bsfconception/WT32-SC01/Cases/V1.0/holder/Readme.md

The SVG file is ready to be cut by a CO2 laser

The design is ready for 3mm Acrylic sheet
