bsfconception/WT32-SC01/Cases/V1.0/3DPrint/readme.md

There 3 files are clean and compatible with Cura or Repetier slicer.
It includes 
- the main enclure 
- the back cover
- the washer between the WT32 and expansion board


Note : the washers are designed to fit to the brass inserts as shown in the picture below
