bsfconception/WT32-SC01/Cases/V1.1/Image3.jpg

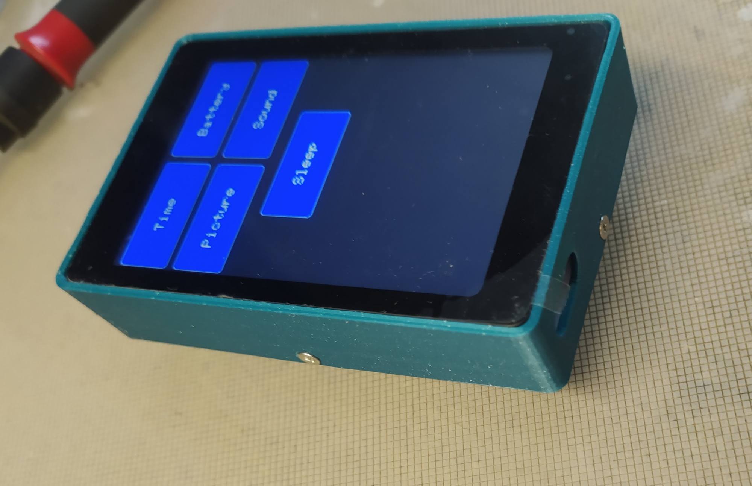
Cases/V1.1/Image3.jpg
