bsfconception/WT32-SC01/Versions/V1.0/PCB/Manufacturing/readme.md

These files have been used to manufacture the PCB usong JLCPCB services
