bsfconception/WT32-SC01/Versions/V1.2/Schematic/WT32-SC01.V1.2_Shematic.pdf

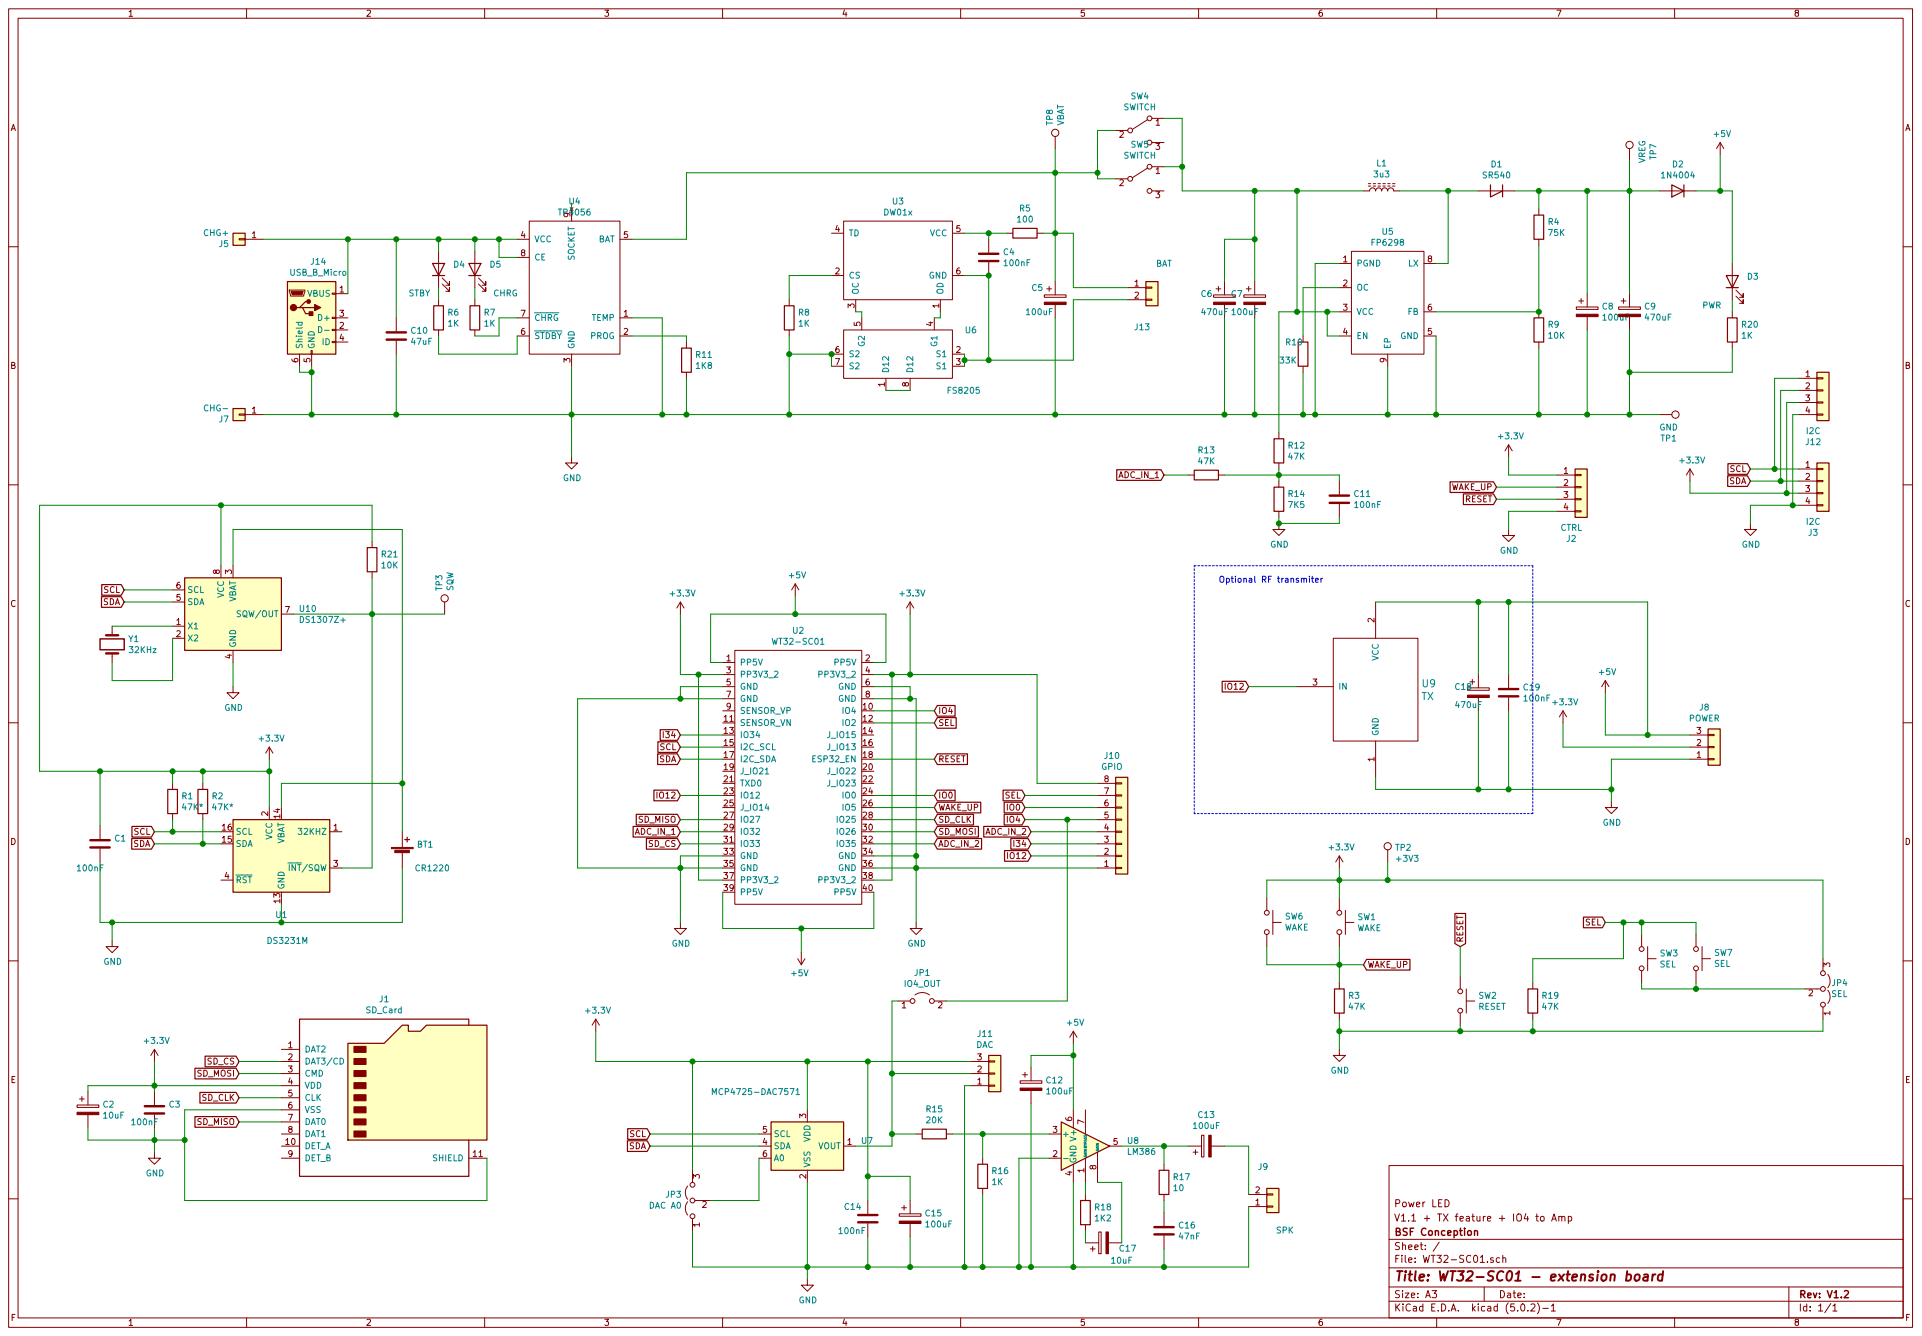
[picture p38: page 1]

3 VCC 4 BAT 5 STDBY 6 CHRG 7 CE 8 SOCKET

8 U6 FS8205 PGND 1 OC 2 VCC 3 EN 4 GND 5 FB 6

4 SDA 5 SCL 6 SQW/OUT 7 VCC

V1.1 + TX feature + IO4 to Amp Power LED

File: WT32-SC01.sch Sheet: / BSF Conception

Id: 1/1 Title: WT32-SC01 - extension board
