bsfconception/WT32-SC01/Versions/V1.0/Schematic/WT32-SC01.pdf

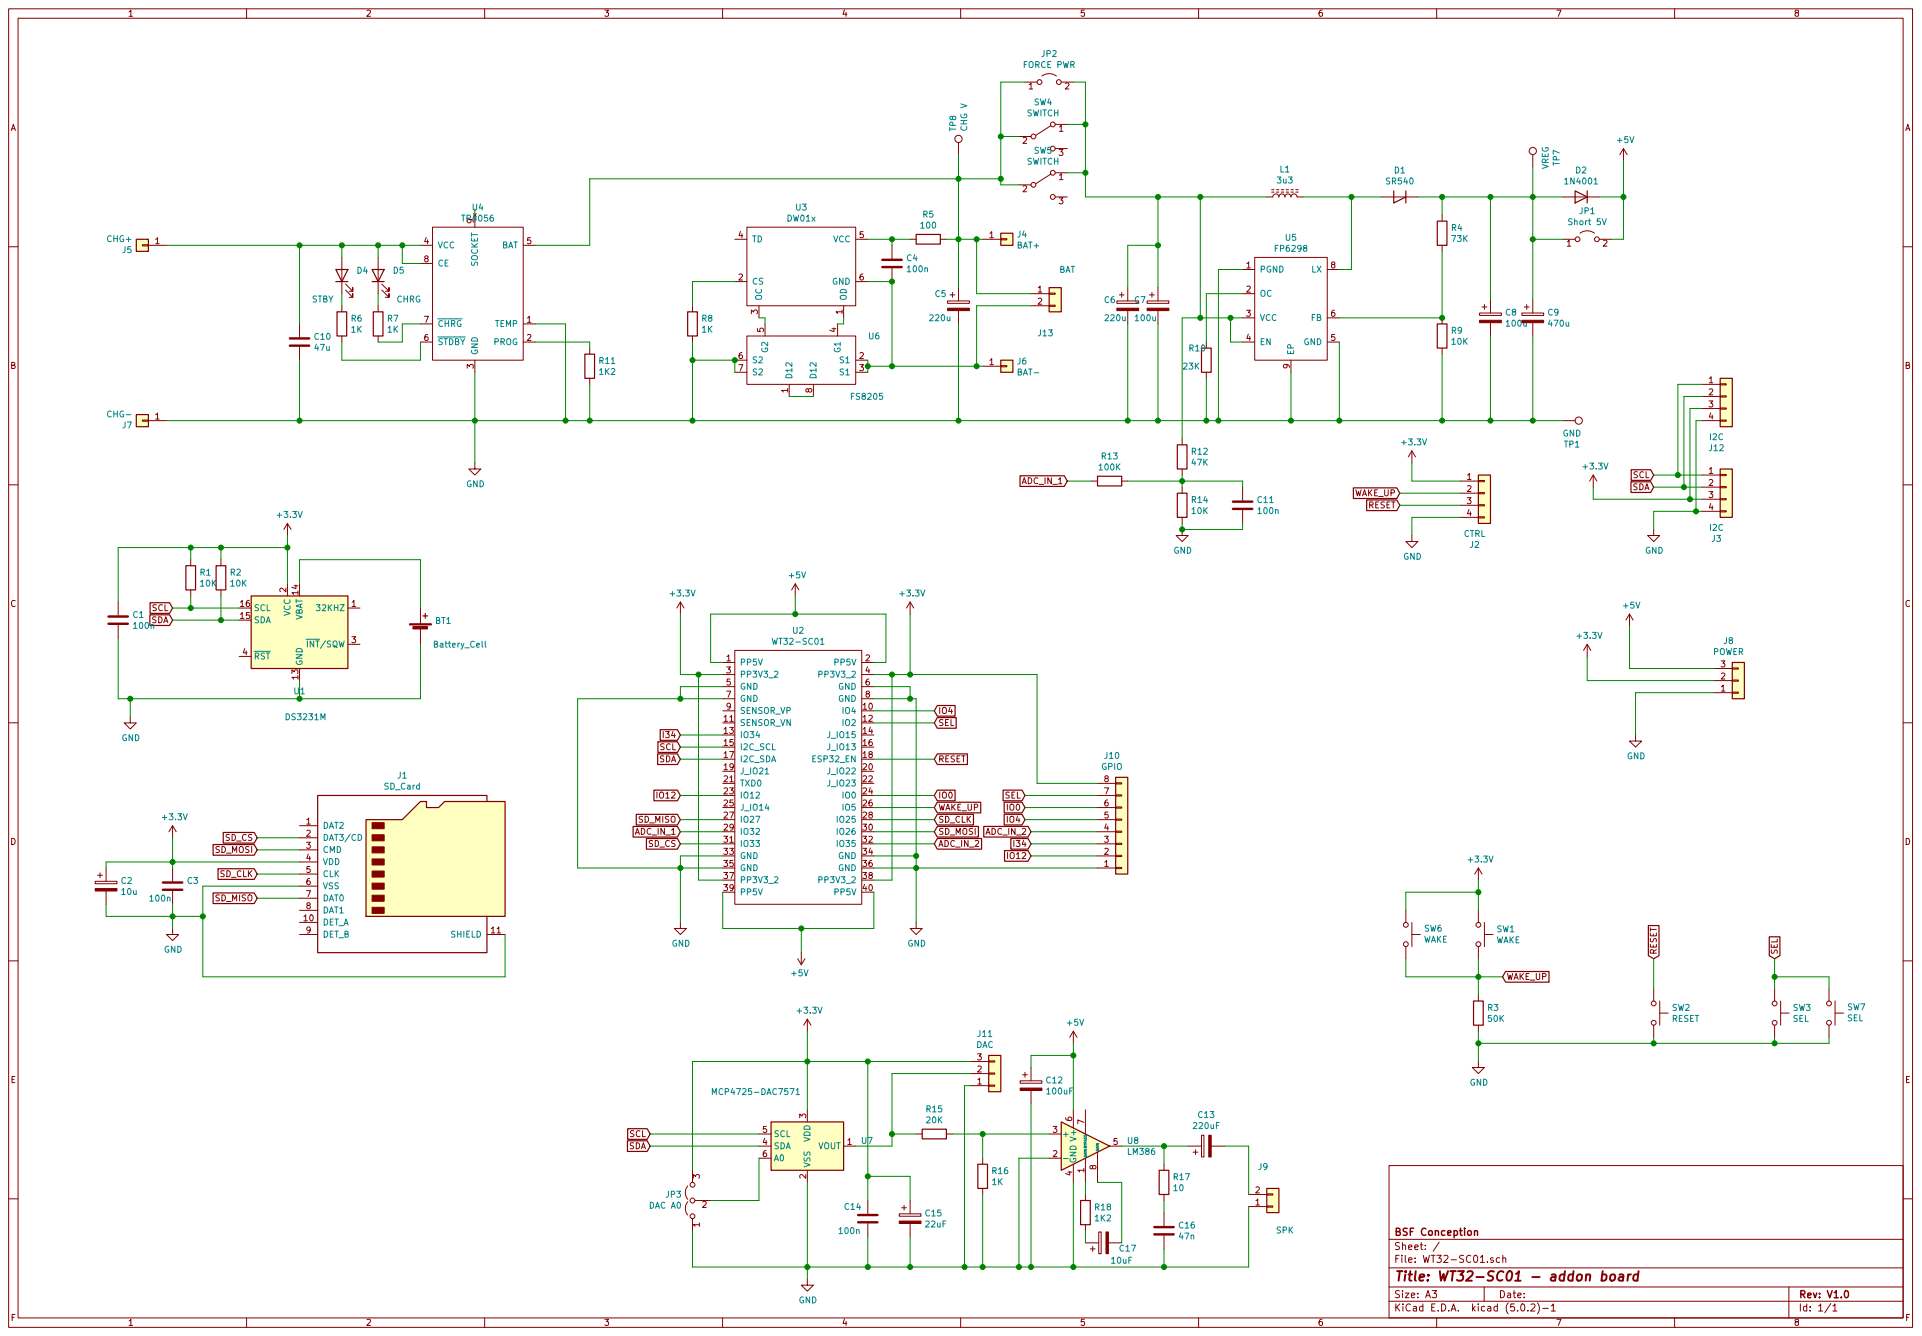
[picture p39: page 1]

File: WT32-SC01.sch Sheet: / BSF Conception

Id: 1/1 Title: WT32-SC01 - addon board
