bsfconception/WT32-SC01/Versions/V1.0/PCB/WT32-SC01-B.SilkS.pdf

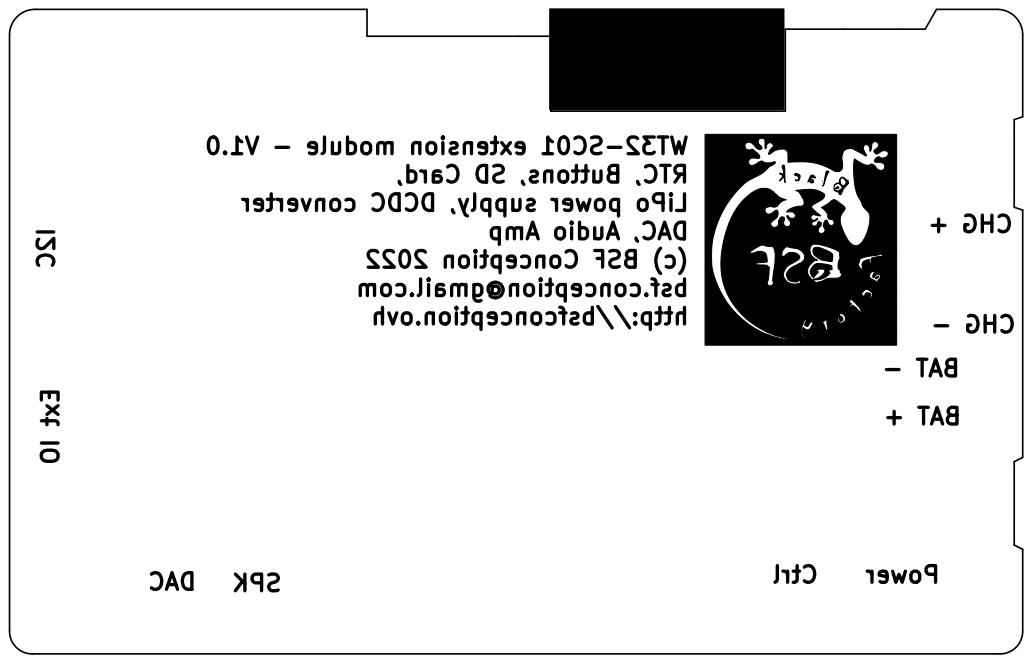
[picture p40: page 1]

DAC SPK Ctrl Power CHG - CHG +BAT - BAT + WT32-SC01 extension module - V1.0 RTC, Buttons, SD Card,

LiPo power supply, DCDC converter

bsf.conception@gmail.com
