bsfconception/WT32-SC01/Versions/V1.2/PCB/WT32-SC01.V1.2_PCB Layout.pdf

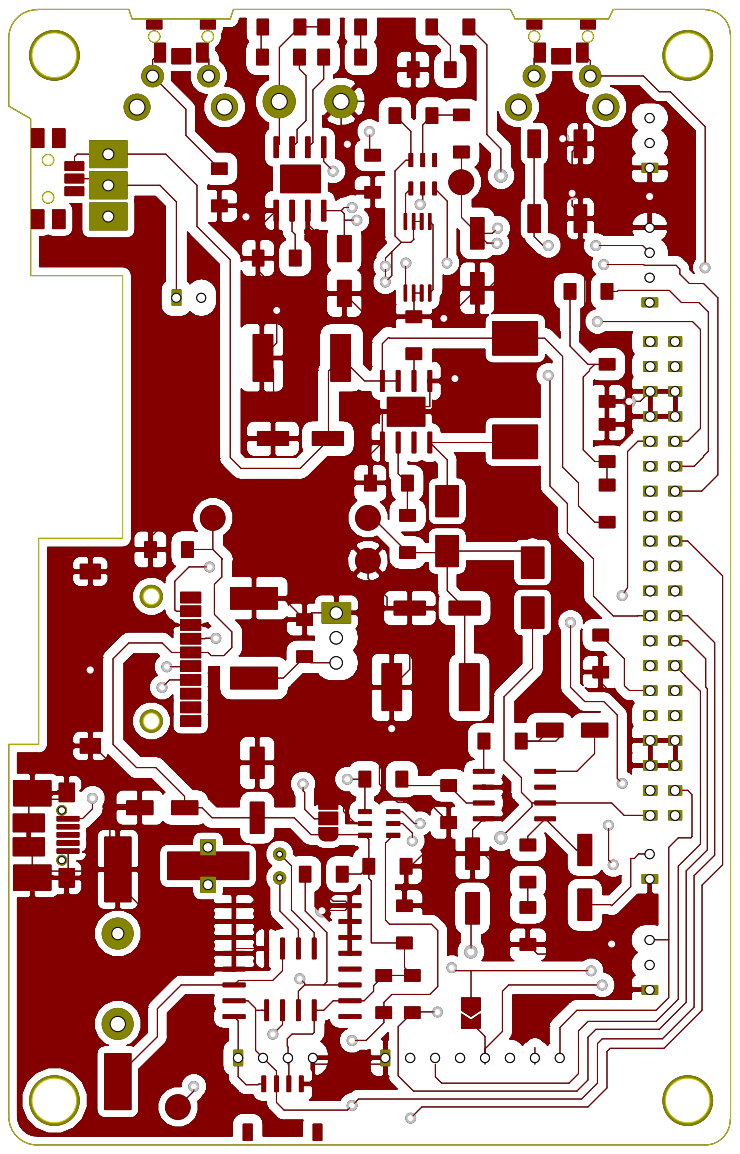
[picture p41: page 1]

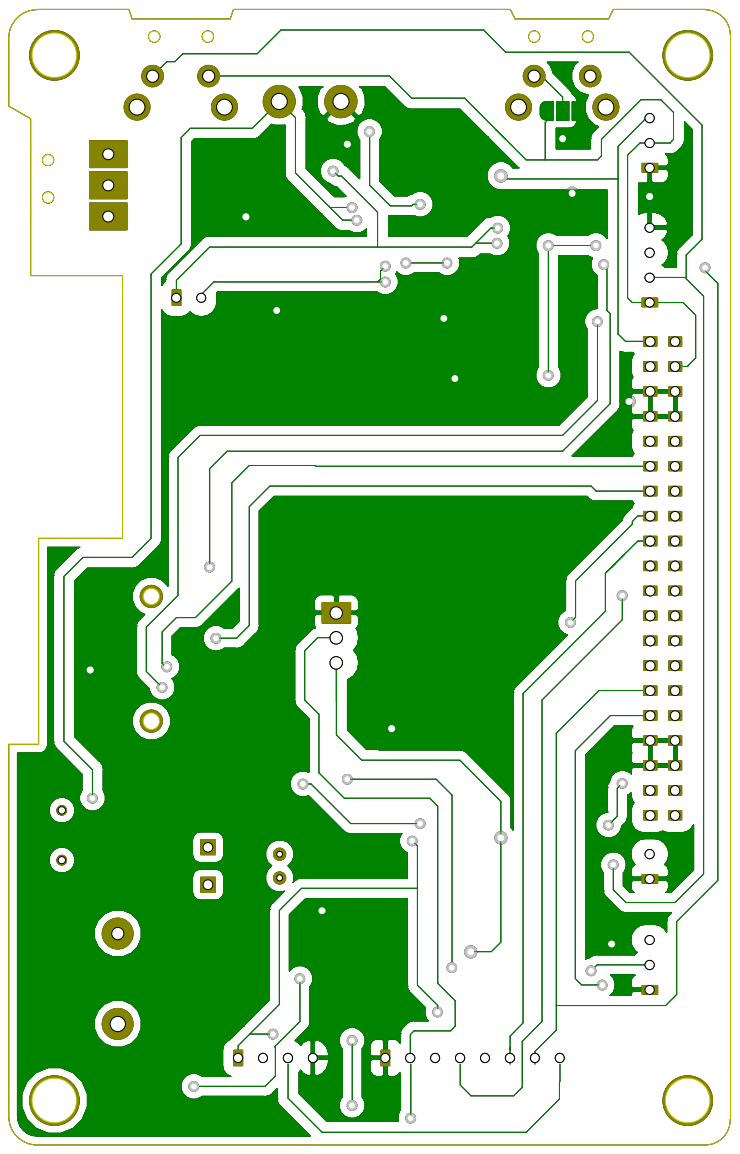
[picture p42: page 2]

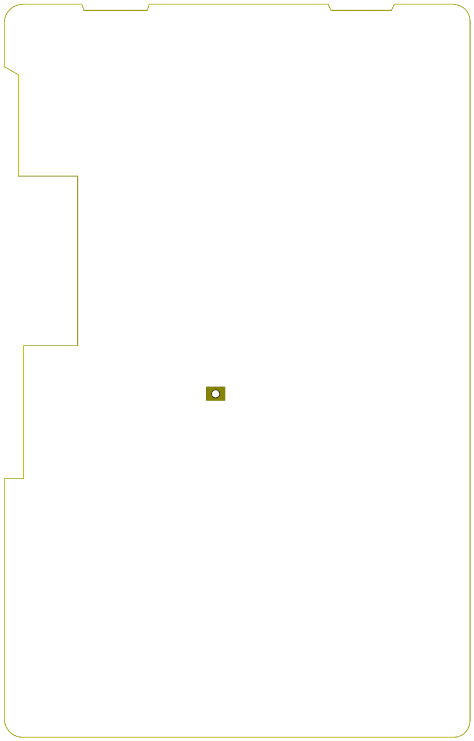
[picture p43: figure]

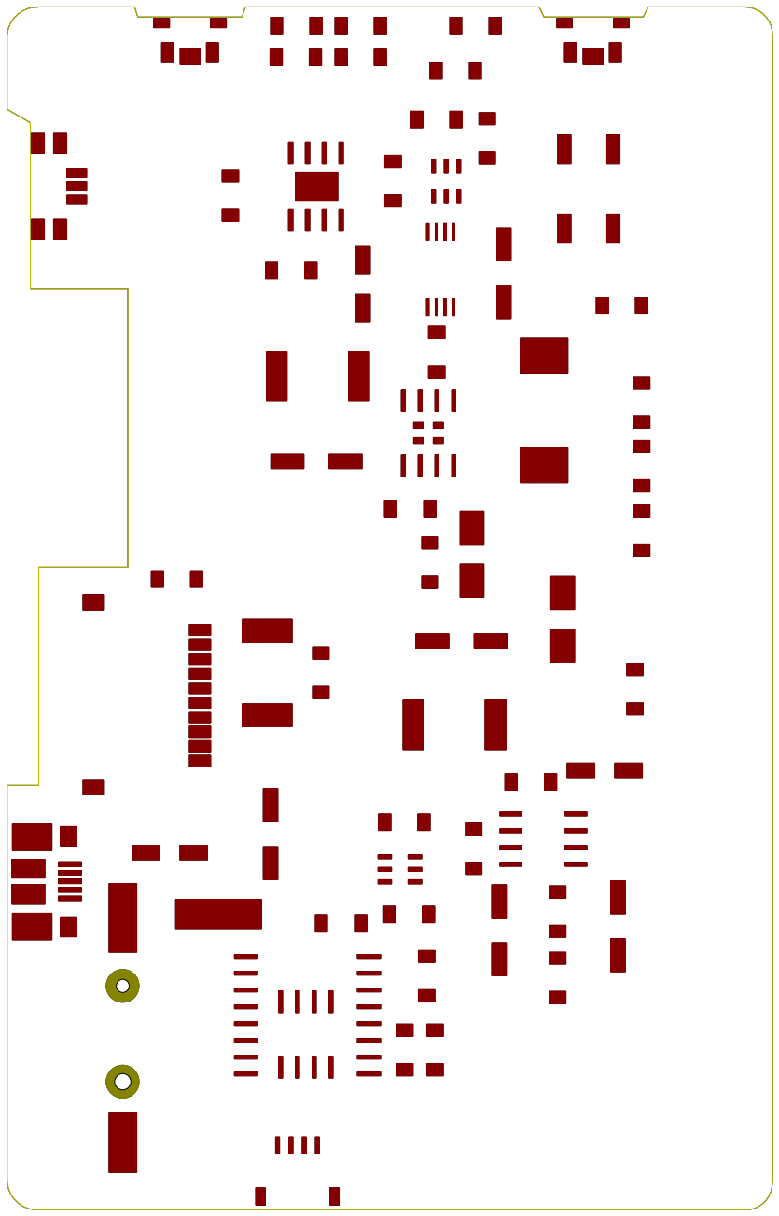
[picture p44: figure]

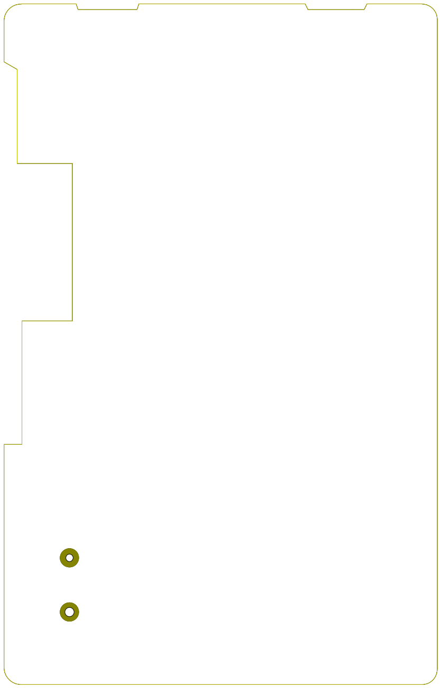
[picture p45: figure]
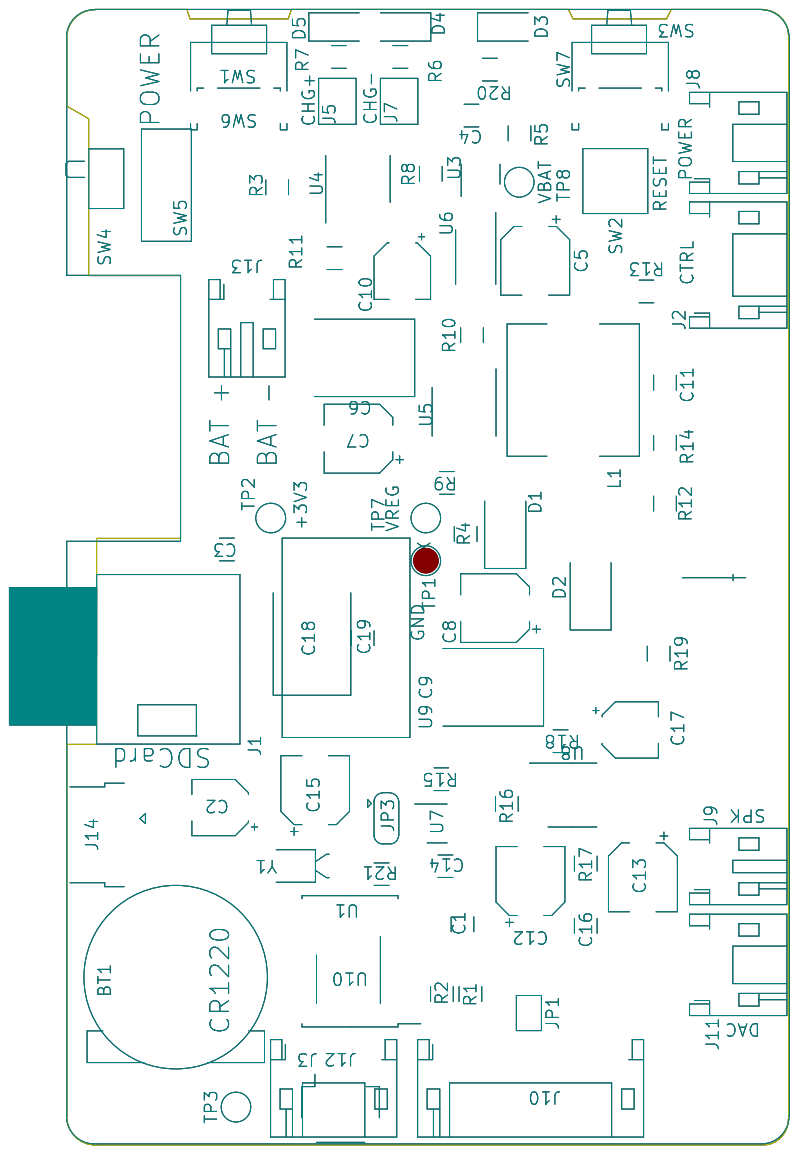
[picture p46: page 7]

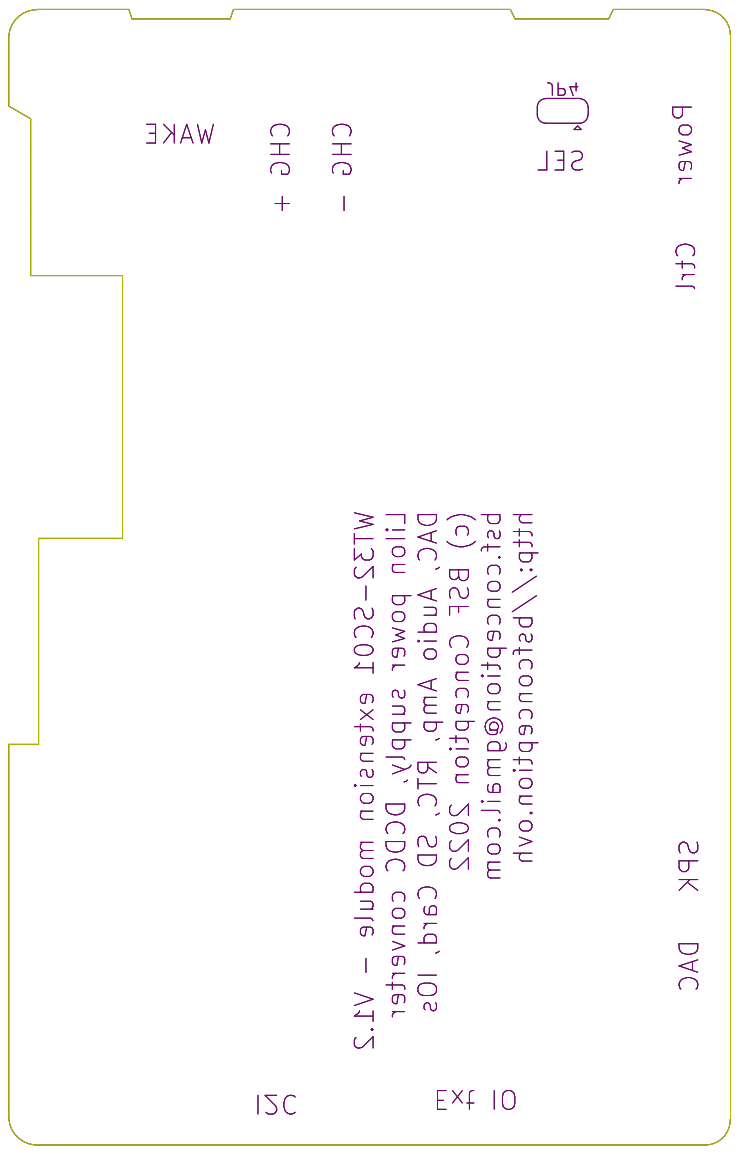
[picture p47: page 8]

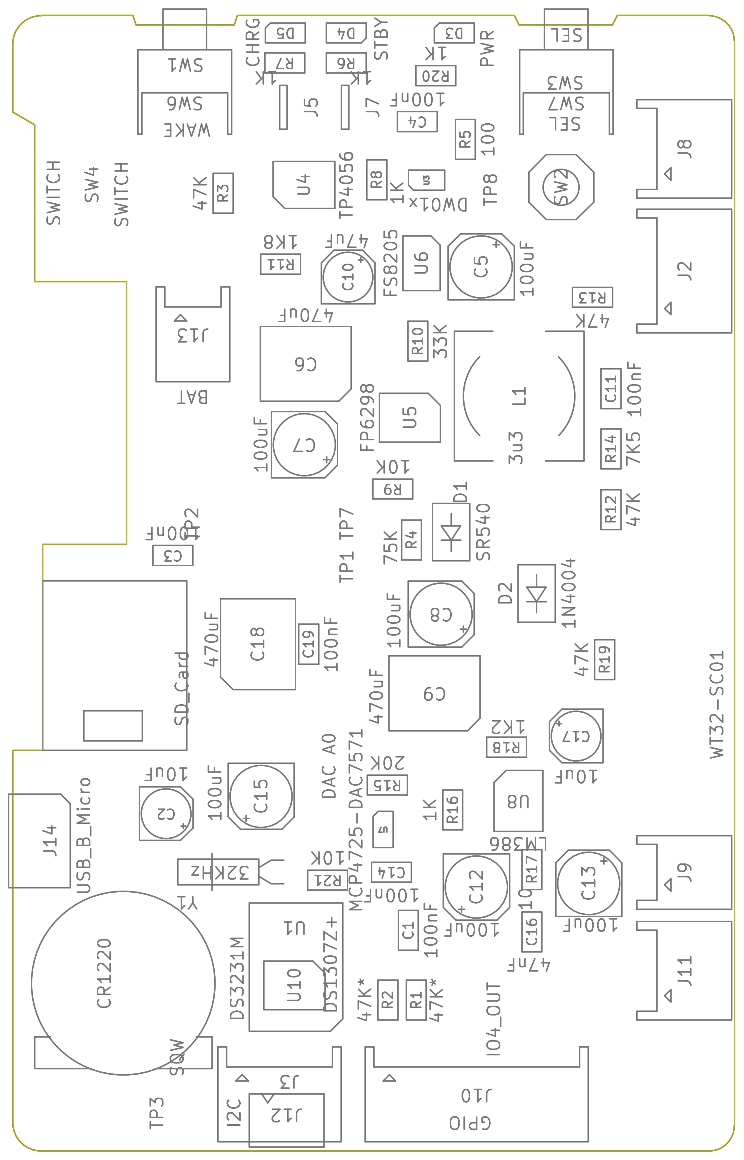
[picture p48: page 9]
