bsfconception/WT32-SC01/Versions/V1.1/PCB/WT32-SC01-F.Fab.pdf

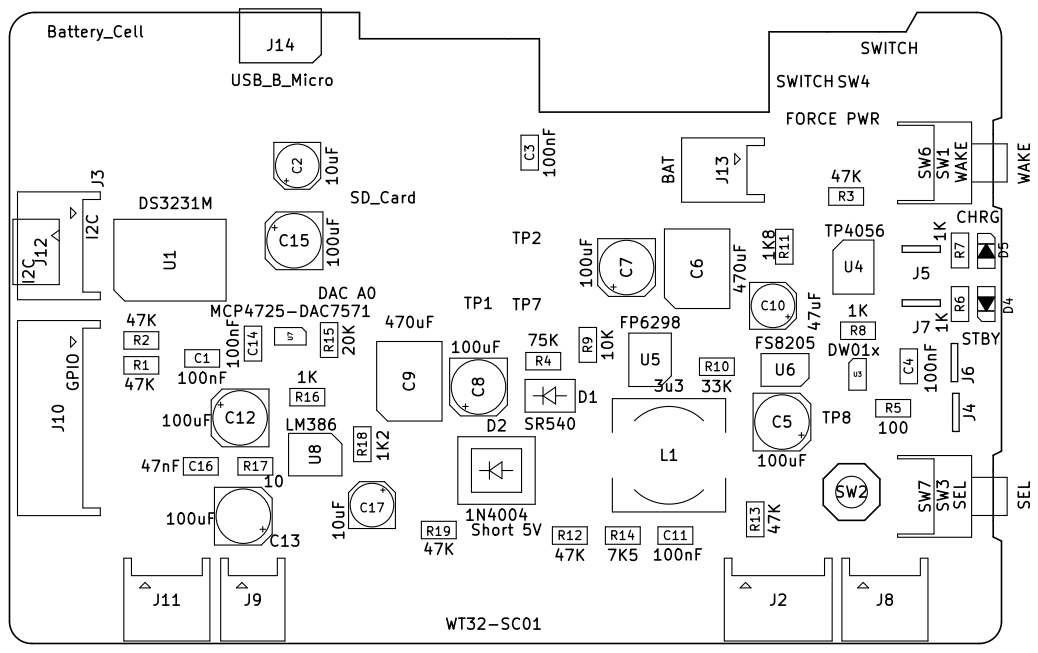
[picture p49: page 1]
