bsfconception/WT32-SC01/Versions/V1.1/PCB/WT32-SC01-B.Cu.pdf

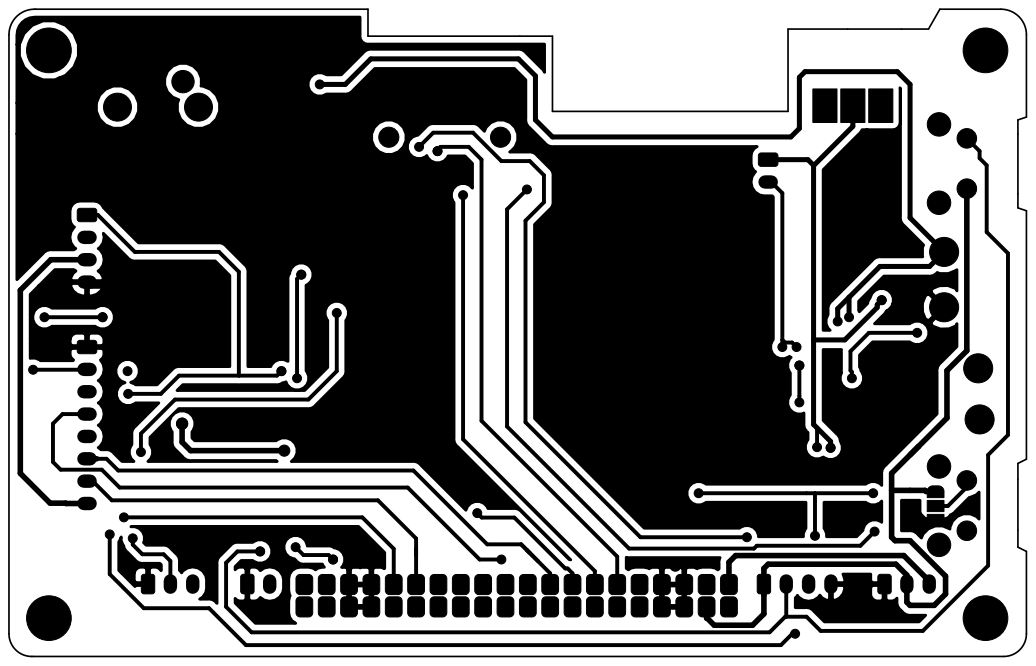
[picture p50: page 1]
