bsfconception/WT32-SC01/Versions/V1.1/PCB/WT32-SC01-F.Cu.pdf

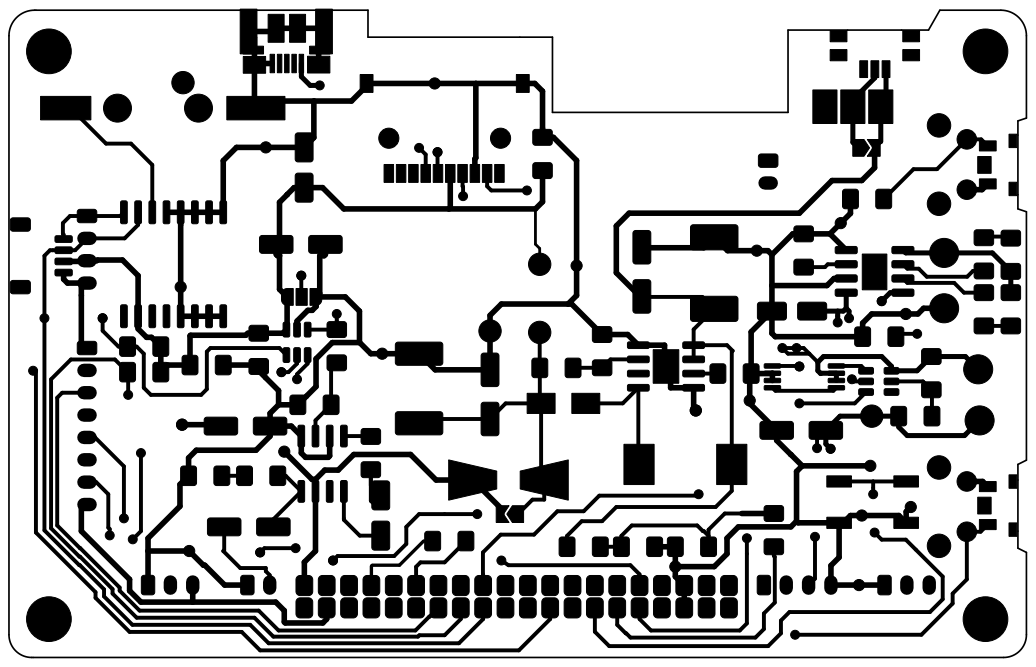
[picture p51: page 1]
