bsfconception/WT32-SC01/Versions/V1.1/PCB/WT32-SC01-F.Mask.pdf

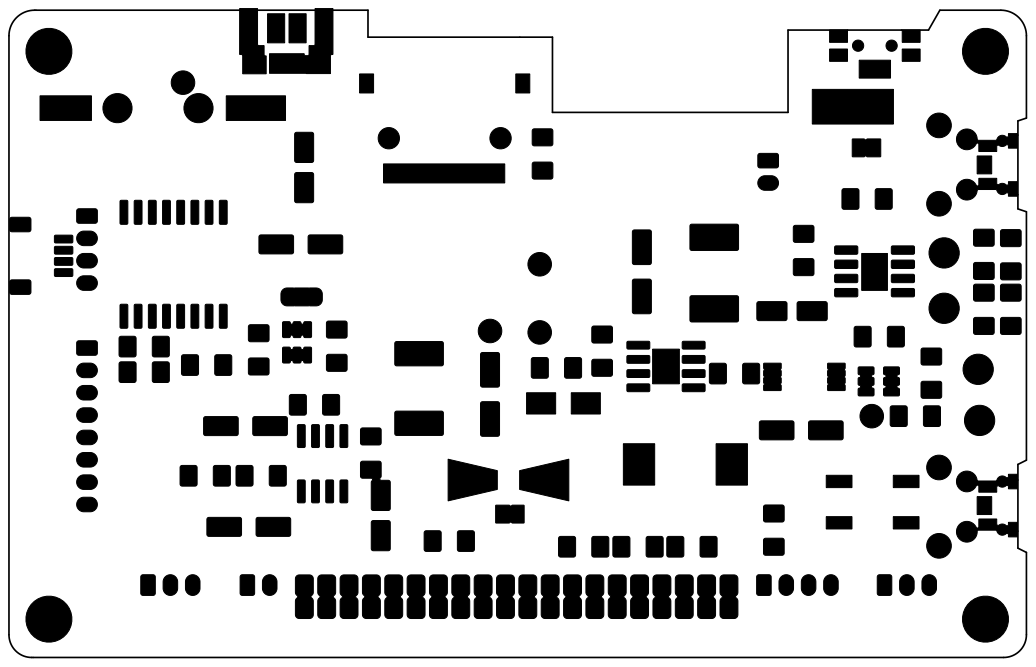
[picture p52: page 1]
