bsfconception/WT32-SC01/Versions/V1.1/PCB/WT32-SC01-F.Paste.pdf

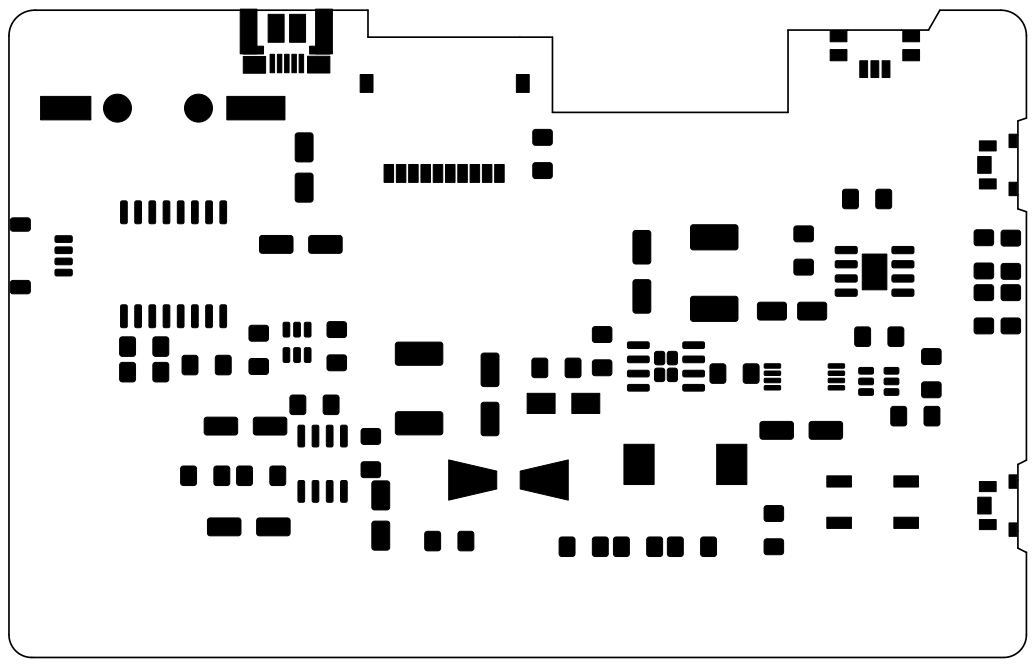
[picture p53: page 1]
