bsfconception/WT32-SC01/Versions/V1.1/PCB/WT32-SC01-F.SilkS.pdf

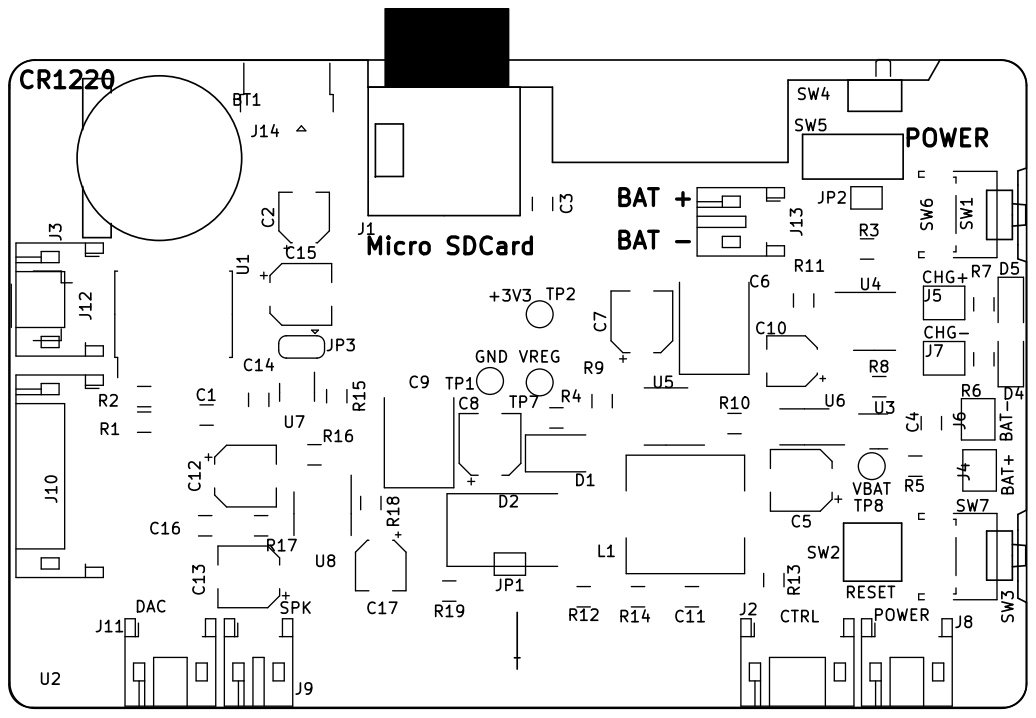
[picture p54: page 1]
