bsfconception/WT32-SC01/Versions/V1.0/PCB/WT32-SC01-B.Cu.pdf

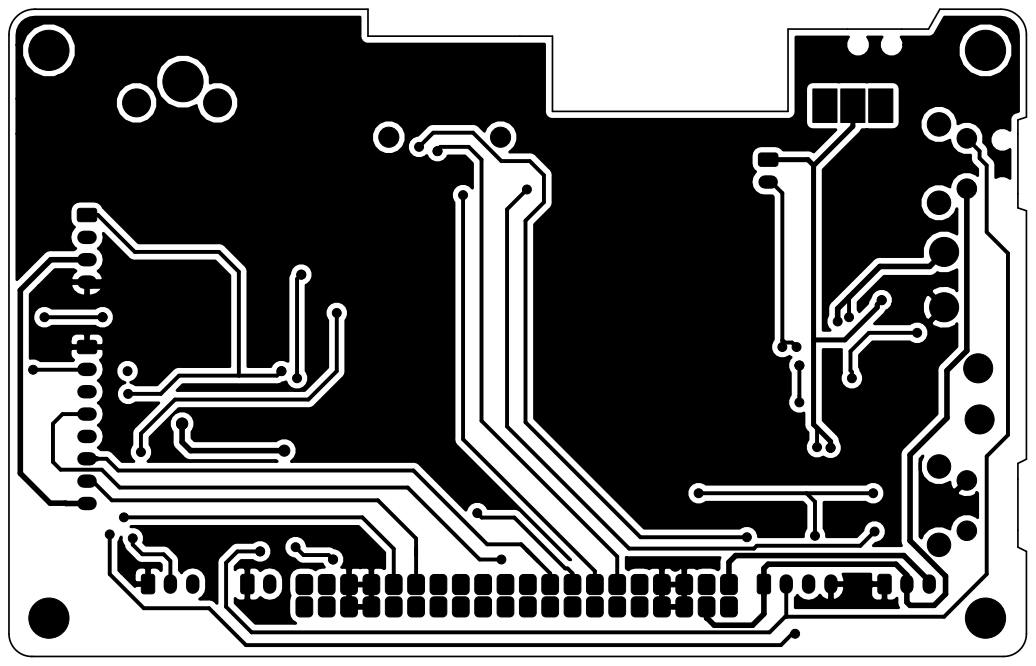
[picture p55: page 1]
