bsfconception/WT32-SC01/Versions/V1.0/PCB/WT32-SC01-Edge.Cuts.pdf

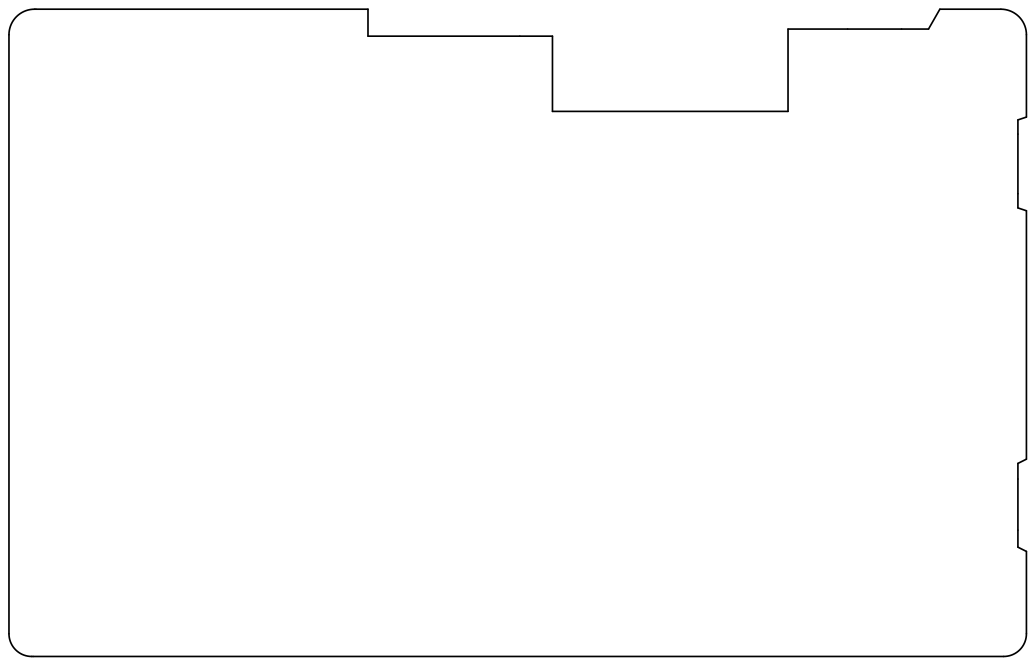
[picture p56: page 1]
