bsfconception/WT32-SC01/Versions/V1.0/PCB/WT32-SC01-F.Cu.pdf

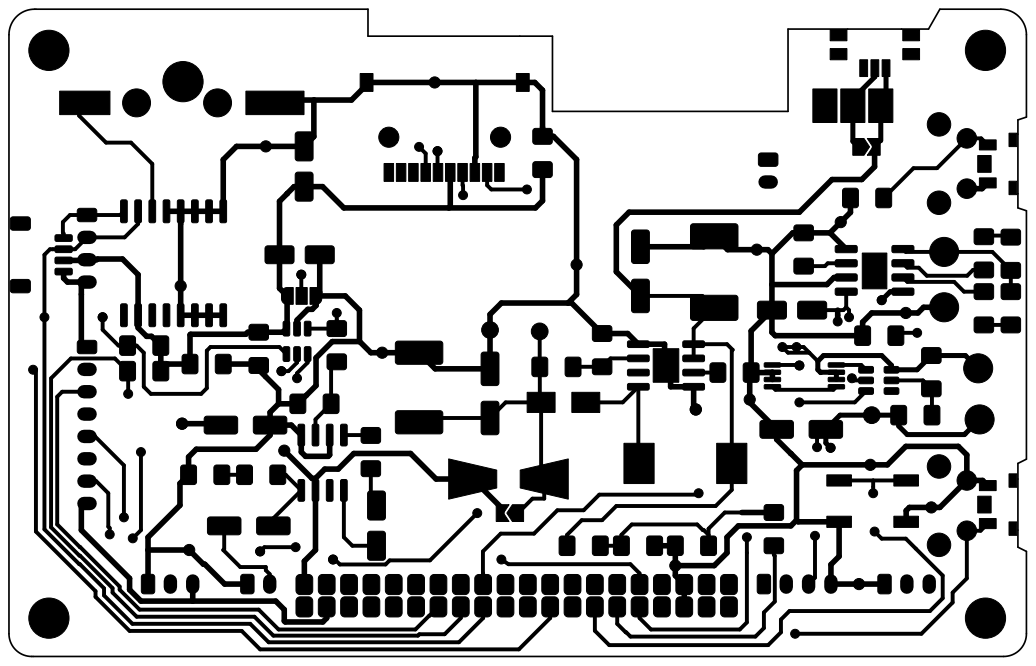
[picture p57: page 1]
