bsfconception/WT32-SC01/Versions/V1.0/PCB/WT32-SC01-F.SilkS.pdf

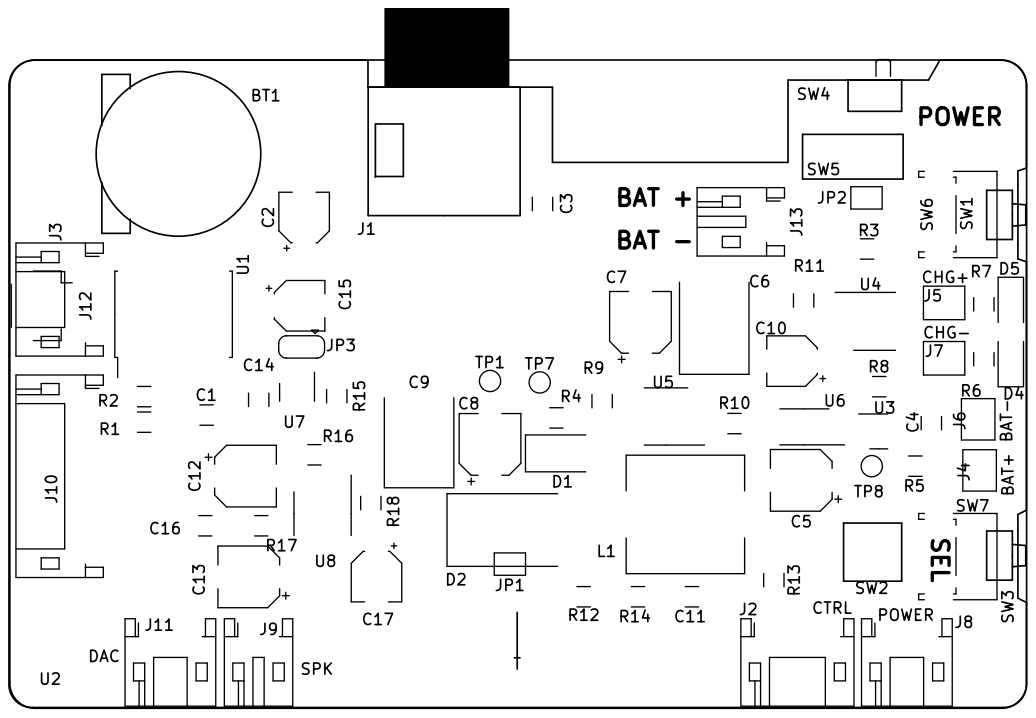
[picture p58: page 1]
