bsfconception/WT32-SC01/Versions/V1.0/PCB/WT32-SC01-placement.pdf

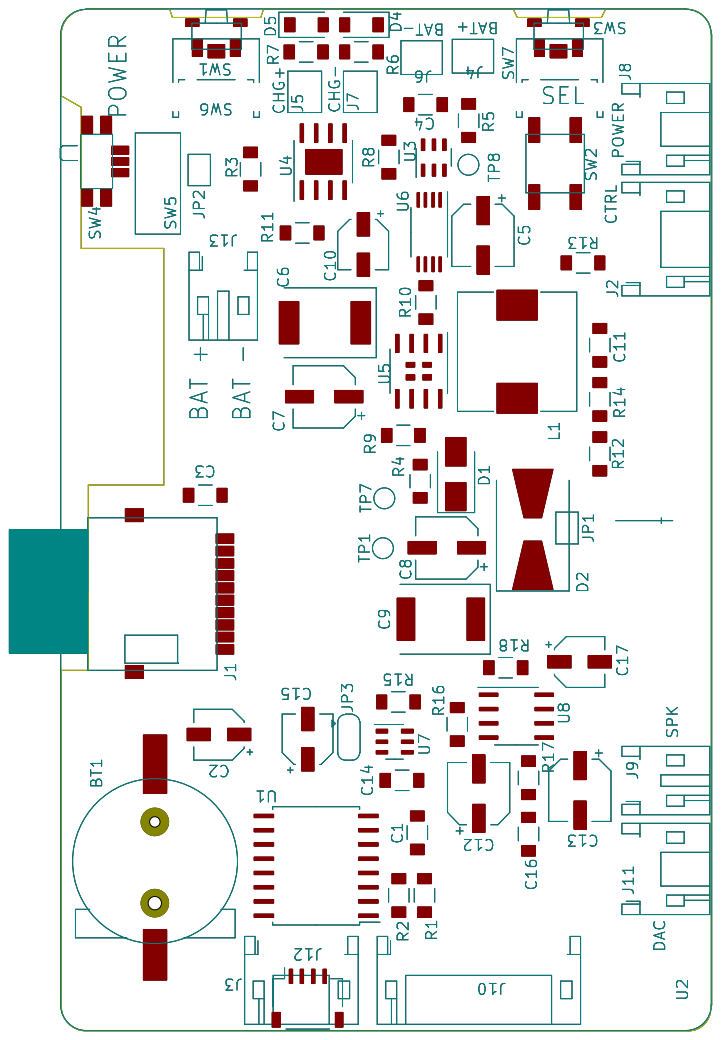
[picture p59: page 1]
